noritsuna/1bit-CPU/images/inverter_circuit.png

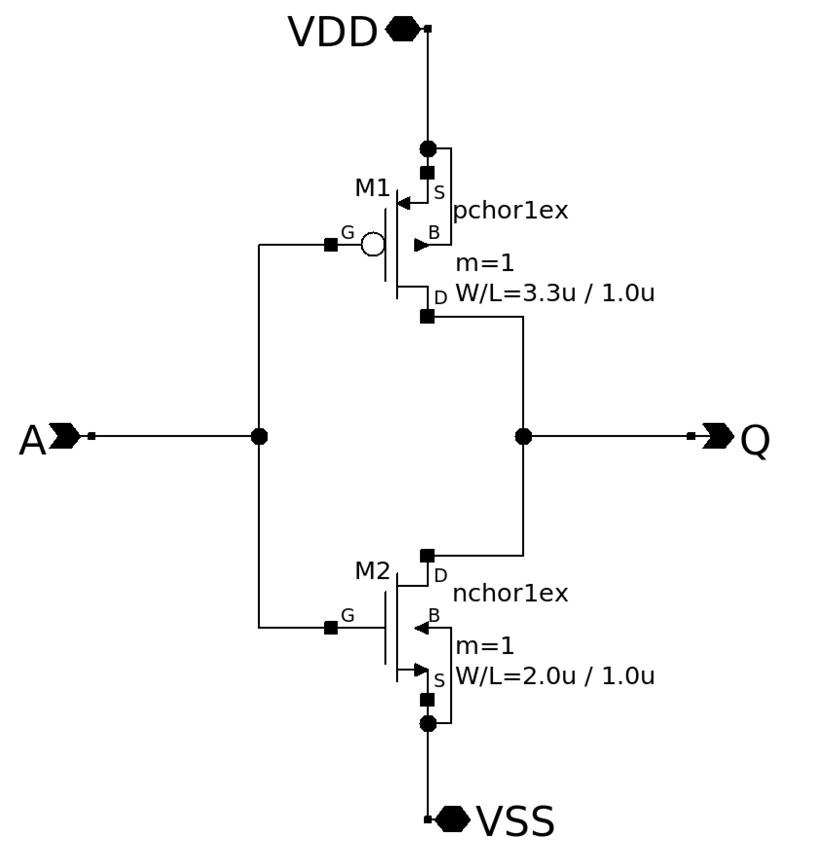
images/inverter_circuit.png
